TrulyVagabond/Vashtastic/assets/First-CAD-nobutton.png

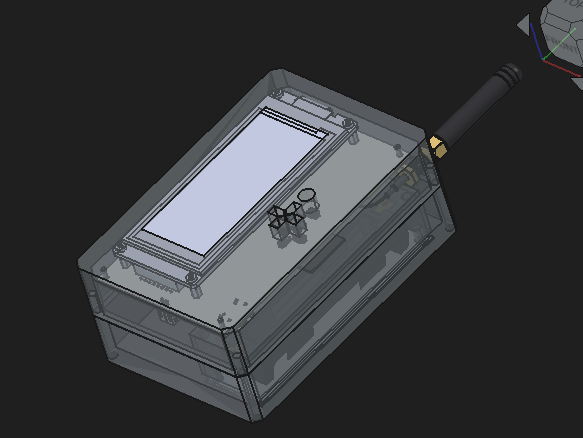
assets/First-CAD-nobutton.png
