TrulyVagabond/Vashtastic/assets/Vashtastic2.png

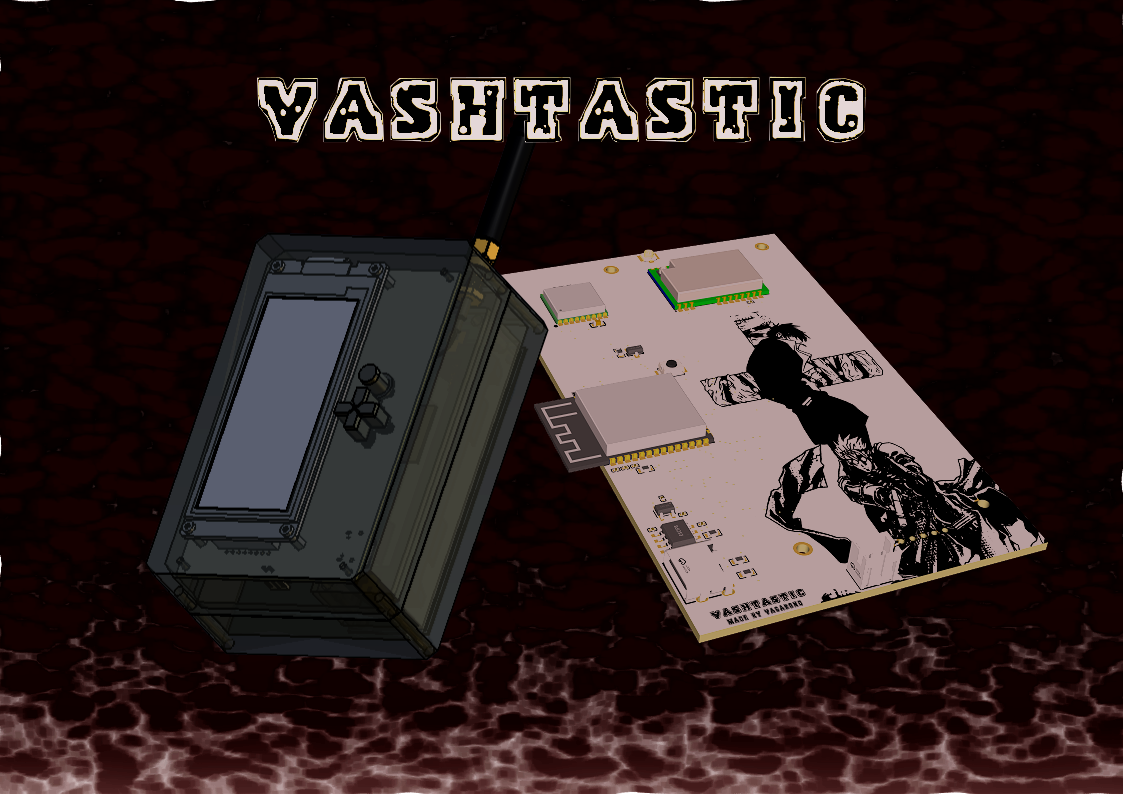
assets/Vashtastic2.png
