TrulyVagabond/Vashtastic/others/GPS.png

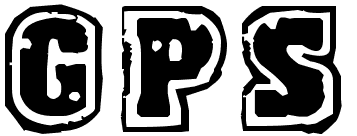
others/GPS.png
