TrulyVagabond/Vashtastic/others/LoRa.png

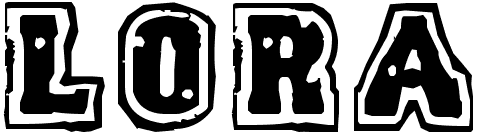
others/LoRa.png
