TrulyVagabond/Vashtastic/others/USB-C-dumbahh.png

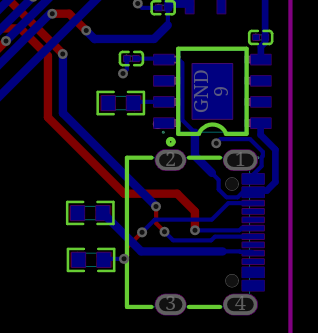
others/USB-C-dumbahh.png
