TrulyVagabond/Vashtastic/others/Vash2.jpg

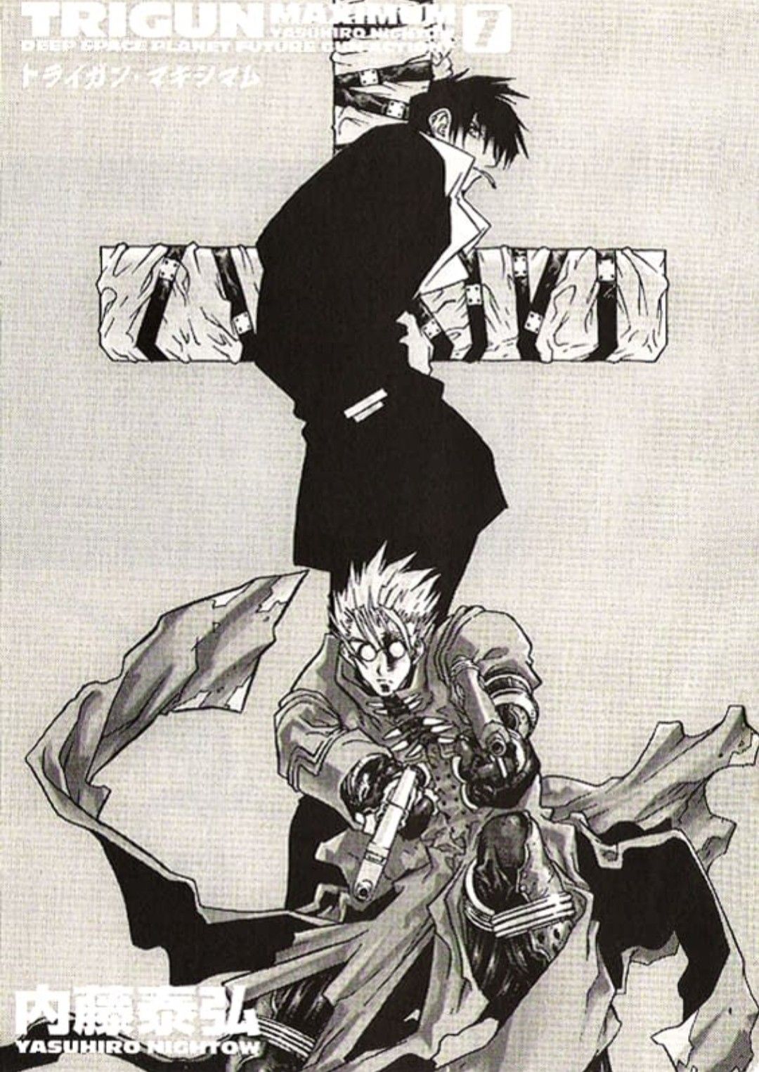
others/Vash2.jpg
