TrulyVagabond/Vashtastic/others/Vash-Vashtastic-PCB.jpg

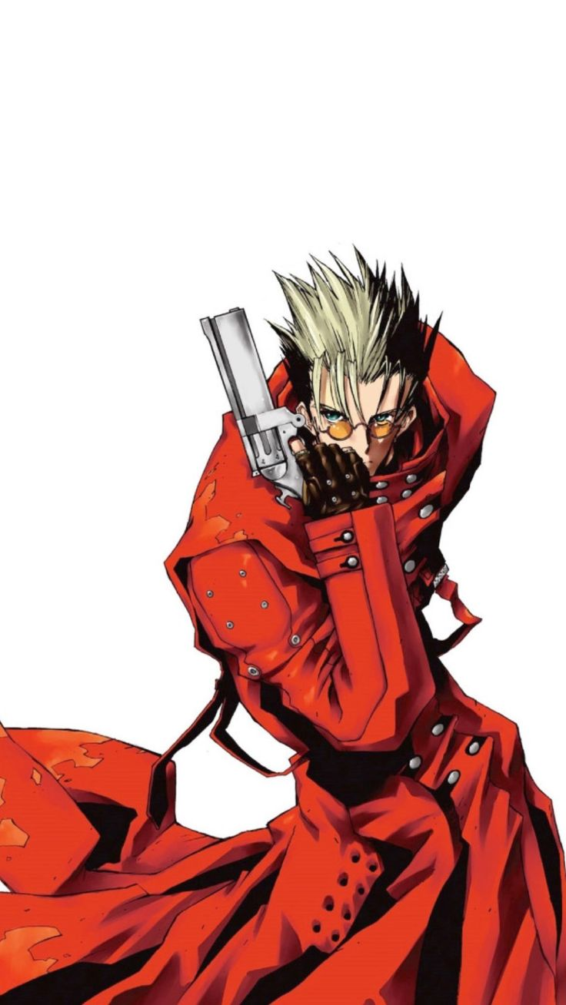
others/Vash-Vashtastic-PCB.jpg
