TrulyVagabond/Vashtastic/others/Vashtastic-pcb.png

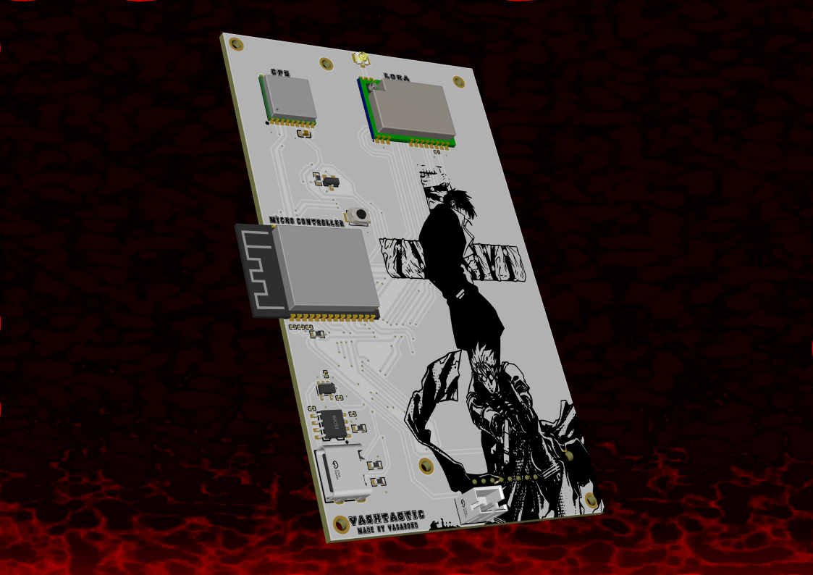
others/Vashtastic-pcb.png
